Musa2004-me/5-DOF-robotic-arm/matlab files/motor_4.png

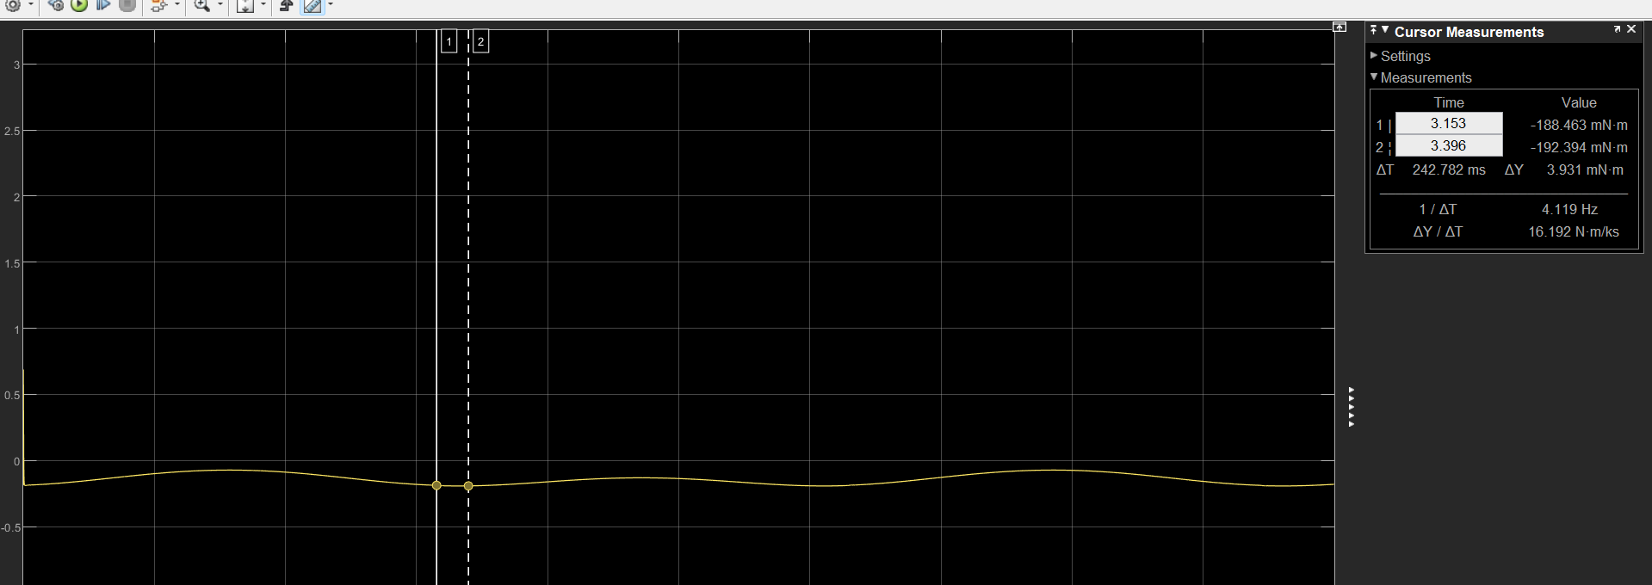
matlab files/motor_4.png
