Musa2004-me/5-DOF-robotic-arm/simplifide for urdf/urdf/All_robot/meshes/l1.STL

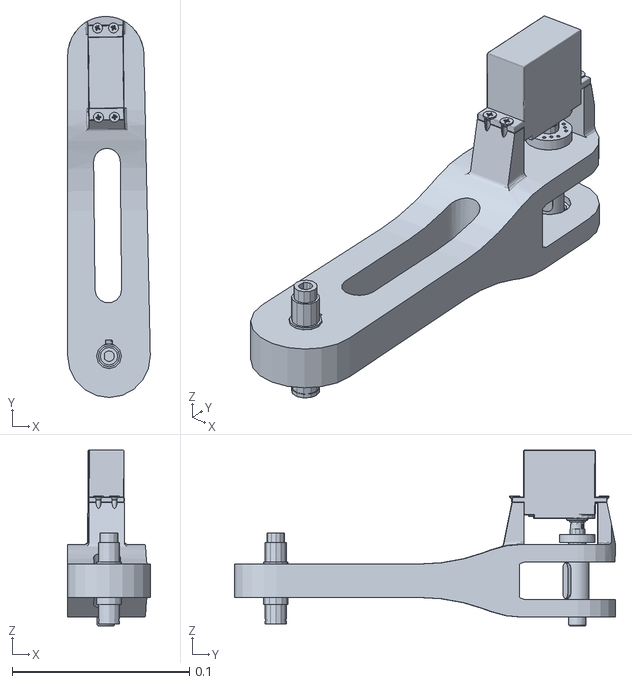
[picture p62: CAD file, 2026-05-22]
simplifide for urdf/urdf/All_robot/meshes/l1.STL
0.0466 x 0.215 x 0.0992
