Musa2004-me/5-DOF-robotic-arm/matlab files/Bidirectional shoulder_Default_sldprt.STEP

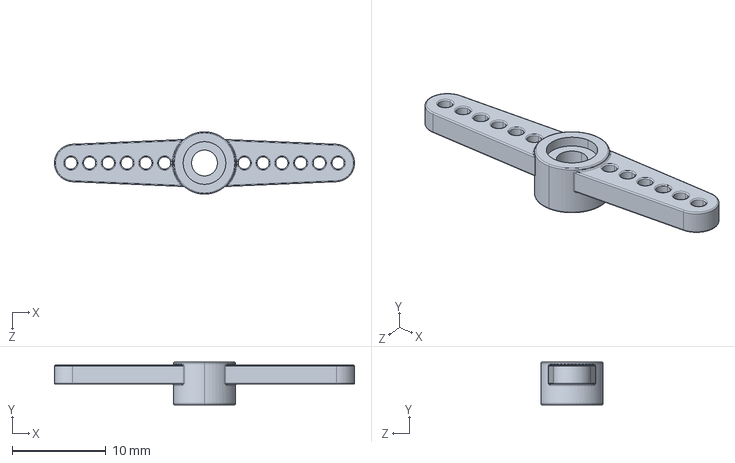
[picture p63: CAD file, 2026-05-22]
matlab files/Bidirectional shoulder_Default_sldprt.STEP
32.0 x 4.55 x 6.65 mm
