Musa2004-me/5-DOF-robotic-arm/simplifide for urdf/scaled2.SLDPRT

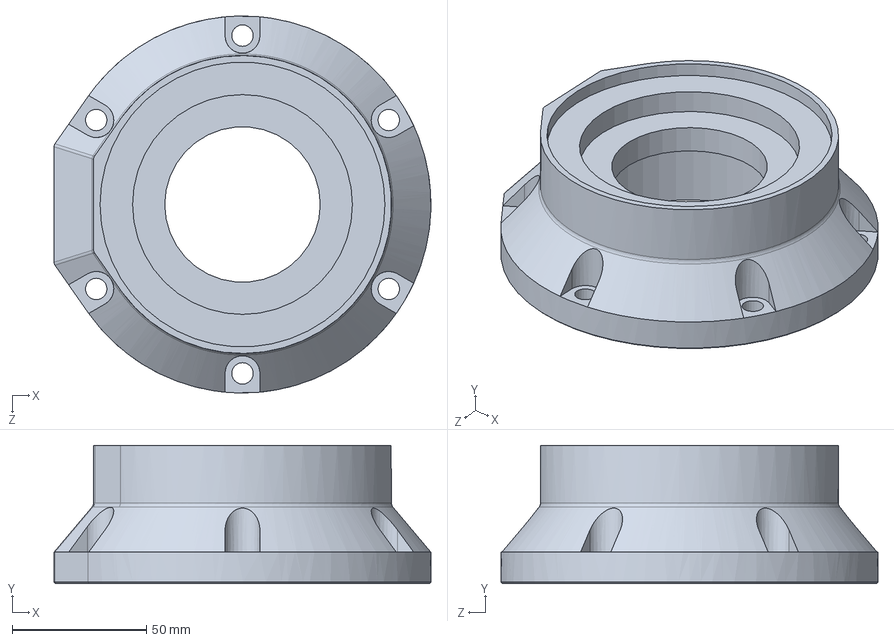
[picture p64: CAD file, 2026-05-22]
simplifide for urdf/scaled2.SLDPRT
140.6 x 51.5 x 140.6 mm
