Musa2004-me/5-DOF-robotic-arm/simplifide for urdf/urdf/All_robot/meshes/l4.STL

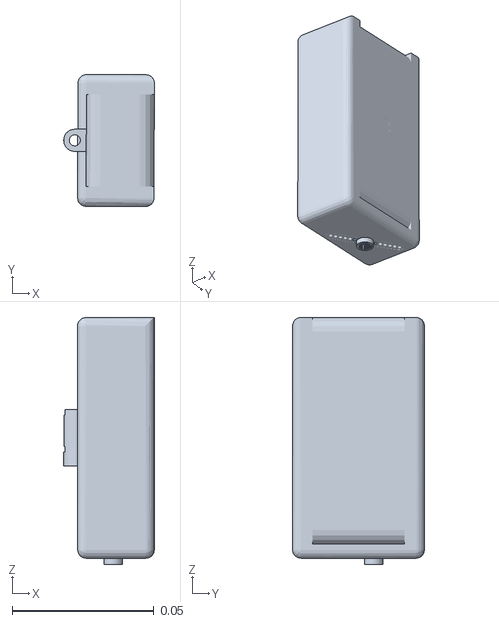
[picture p65: CAD file, 2026-05-22]
simplifide for urdf/urdf/All_robot/meshes/l4.STL
0.0321 x 0.0467 x 0.0872
