Musa2004-me/5-DOF-robotic-arm/simplifide for urdf/link_2.SLDPRT

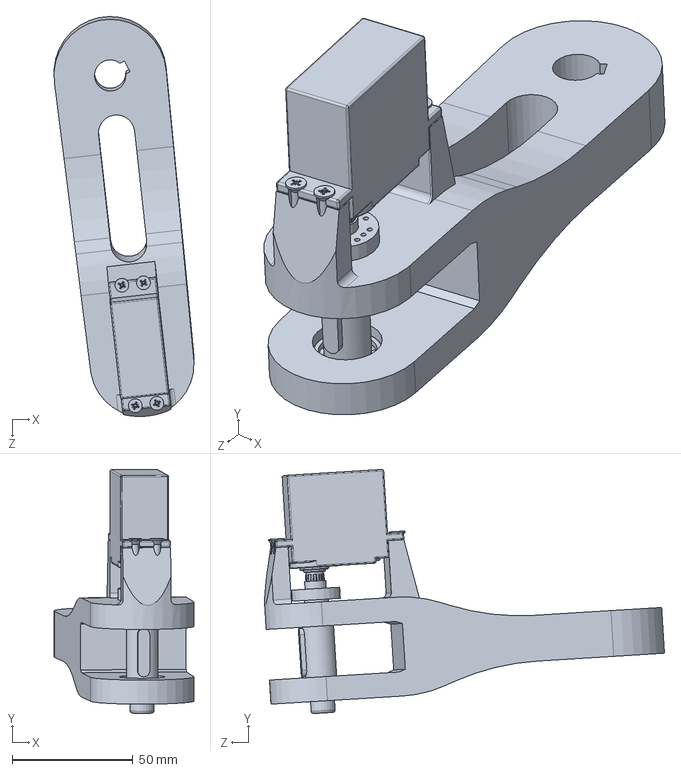
[picture p66: CAD file, 2026-05-22]
simplifide for urdf/link_2.SLDPRT
57.9 x 101.1 x 165.6 mm
