Musa2004-me/5-DOF-robotic-arm/simplifide for urdf/link_1.SLDPRT

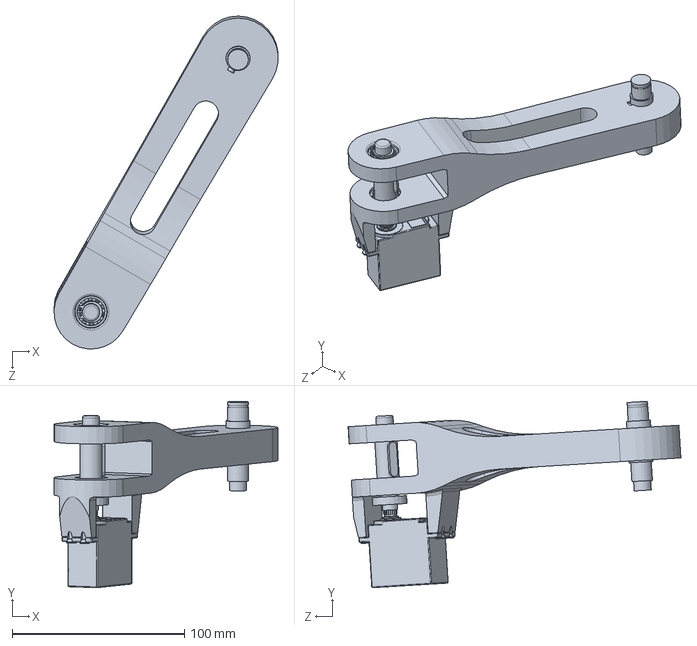
[picture p67: CAD file, 2026-05-22]
simplifide for urdf/link_1.SLDPRT
130.0 x 108.2 x 193.2 mm
