Musa2004-me/5-DOF-robotic-arm/simplifide for urdf/Product stand.SLDPRT

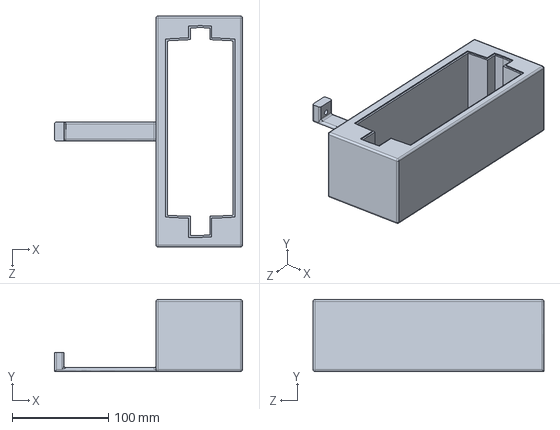
[picture p68: CAD file, 2026-05-22]
simplifide for urdf/Product stand.SLDPRT
195.4 x 75.0 x 240.0 mm
