Musa2004-me/5-DOF-robotic-arm/simplifide for urdf/Bidirectional shoulder.SLDPRT

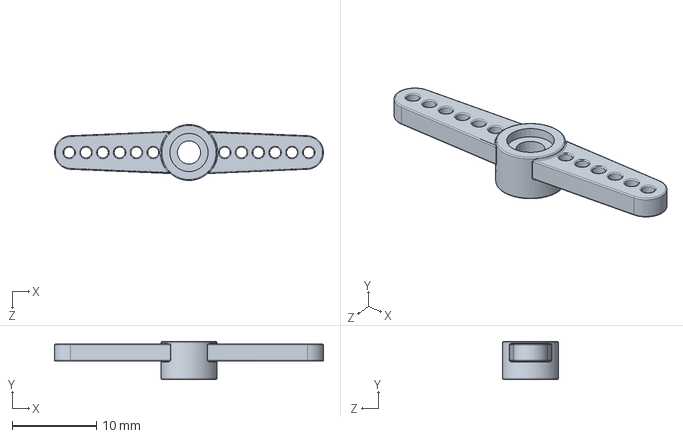
[picture p69: CAD file, 2026-05-22]
simplifide for urdf/Bidirectional shoulder.SLDPRT
32.0 x 4.55 x 6.65 mm
