Musa2004-me/5-DOF-robotic-arm/simplifide for urdf/SHAFT.stp

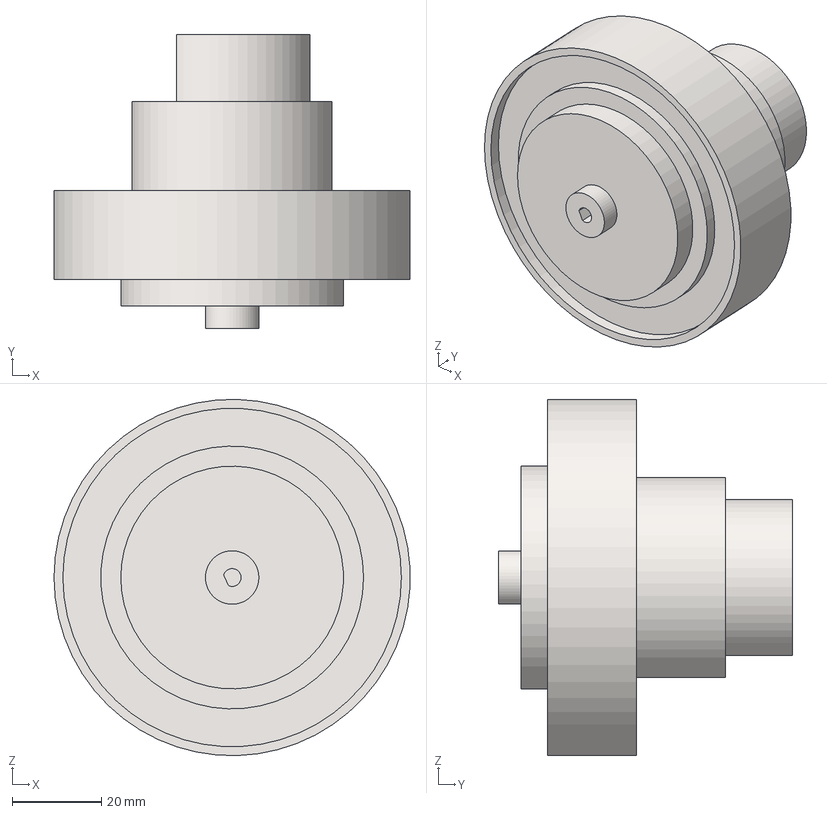
[picture p70: CAD file, 2026-05-22]
simplifide for urdf/SHAFT.stp
79.9 x 66.0 x 80.0 mm
