Musa2004-me/5-DOF-robotic-arm/simplifide for urdf/L joint .stp

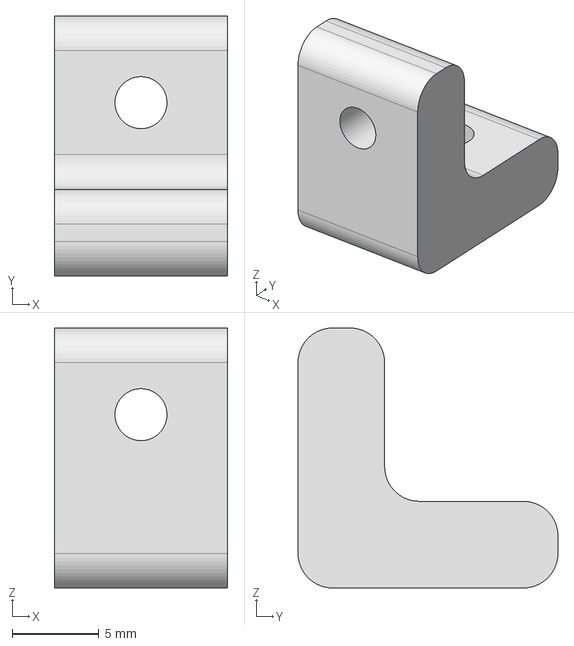
[picture p71: CAD file, 2026-05-22]
simplifide for urdf/L joint .stp
10.0 x 15.0 x 15.0 mm
