Musa2004-me/5-DOF-robotic-arm/simplifide for urdf/BASE.stp

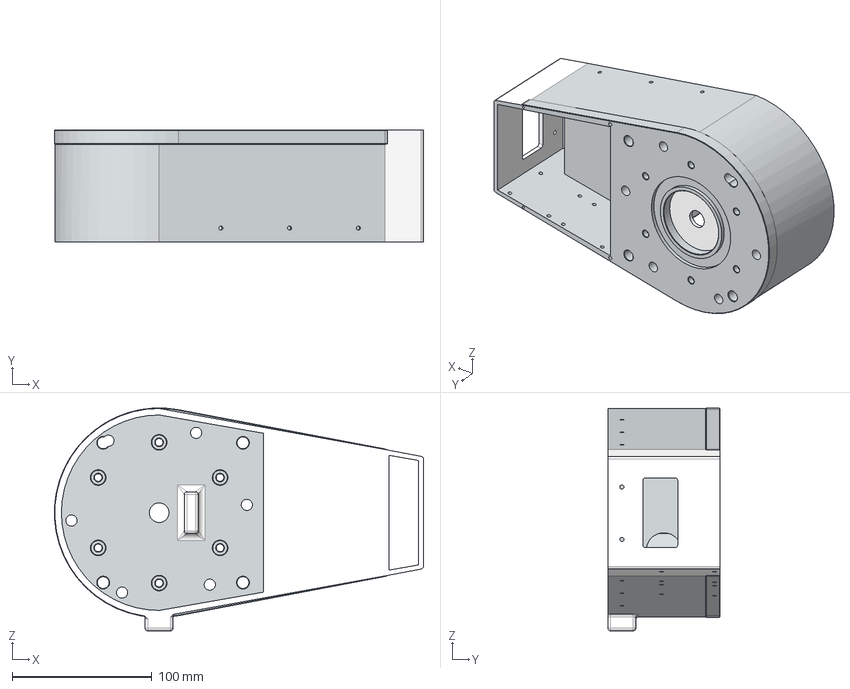
[picture p72: CAD file, 2026-05-22]
simplifide for urdf/BASE.stp
264.0 x 80.3 x 159.5 mm
