Musa2004-me/5-DOF-robotic-arm/simplifide for urdf/link_3.SLDPRT

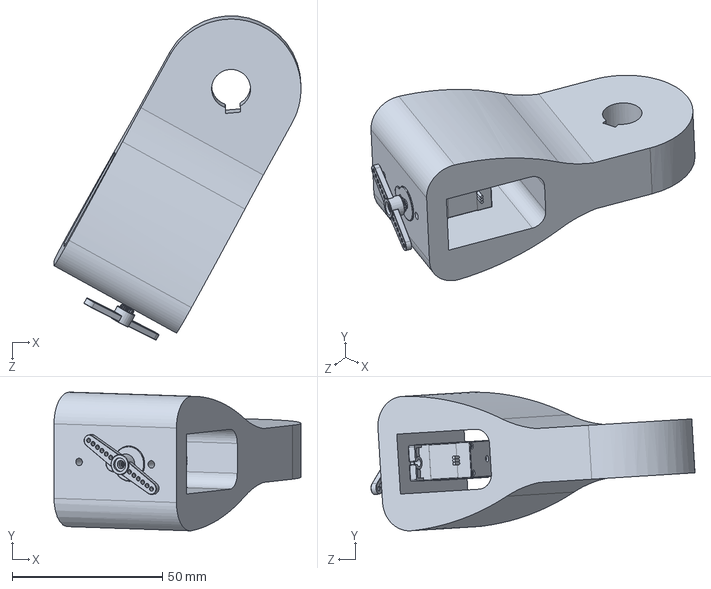
[picture p73: CAD file, 2026-05-22]
simplifide for urdf/link_3.SLDPRT
82.3 x 46.2 x 108.0 mm
