Musa2004-me/5-DOF-robotic-arm/simplifide for urdf/All_robot.SLDASM

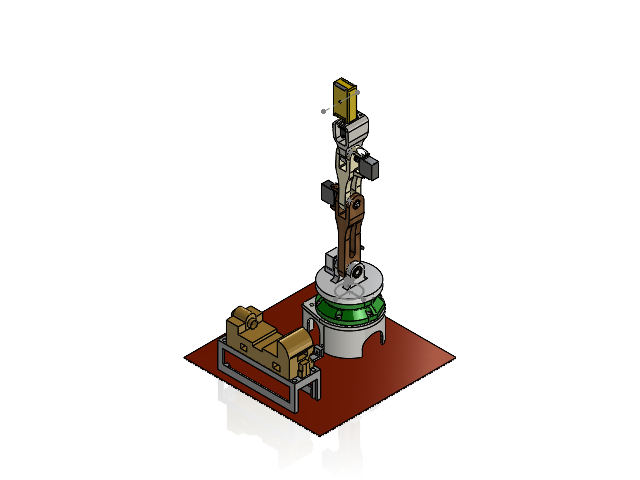
[picture p74: CAD file, 2026-05-22]
simplifide for urdf/All_robot.SLDASM
link_1
link_2
rotataing_plata_2
Assembly1_defeature
cam
link3
camera
