Musa2004-me/5-DOF-robotic-arm/simplifide for urdf/final.SLDASM

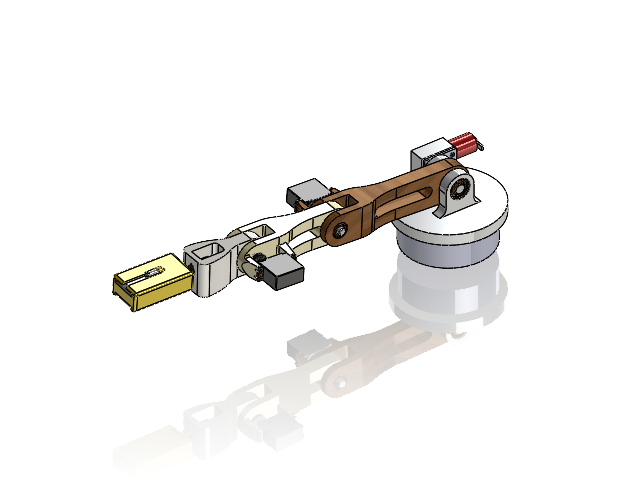
[picture p75: CAD file, 2026-05-22]
simplifide for urdf/final.SLDASM
End_effector
link_1
link_2
link_3
rotataing_plata
Base
Bidirectional shoulder
