Musa2004-me/5-DOF-robotic-arm/simplifide for urdf/casting pattern.SLDASM

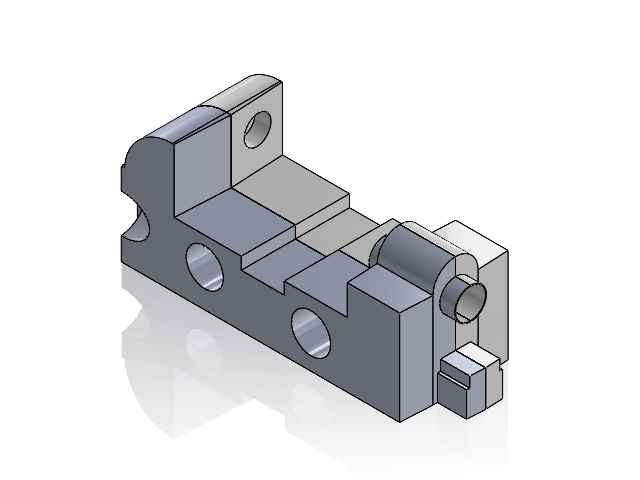
[picture p76: CAD file, 2026-05-22]
simplifide for urdf/casting pattern.SLDASM
Casting Project right.stp
Casting Project left.stp
